devcristi/smartwatch/Core/Inc/main.h

#ifndef MAIN_H#ifndef MAIN_H

#define MAIN_H#define MAIN_H



#define F_CPU 16000000UL// Include necessary headers



#include <avr/io.h>#endif // MAIN_H
#include <avr/interrupt.h>
#include <util/delay.h>
#include <stdint.h>
#include <string.h>

#endif // MAIN_H
